m1geo/Quad-AMBE3000/outputs/AMBE3000R-Devices.jpg

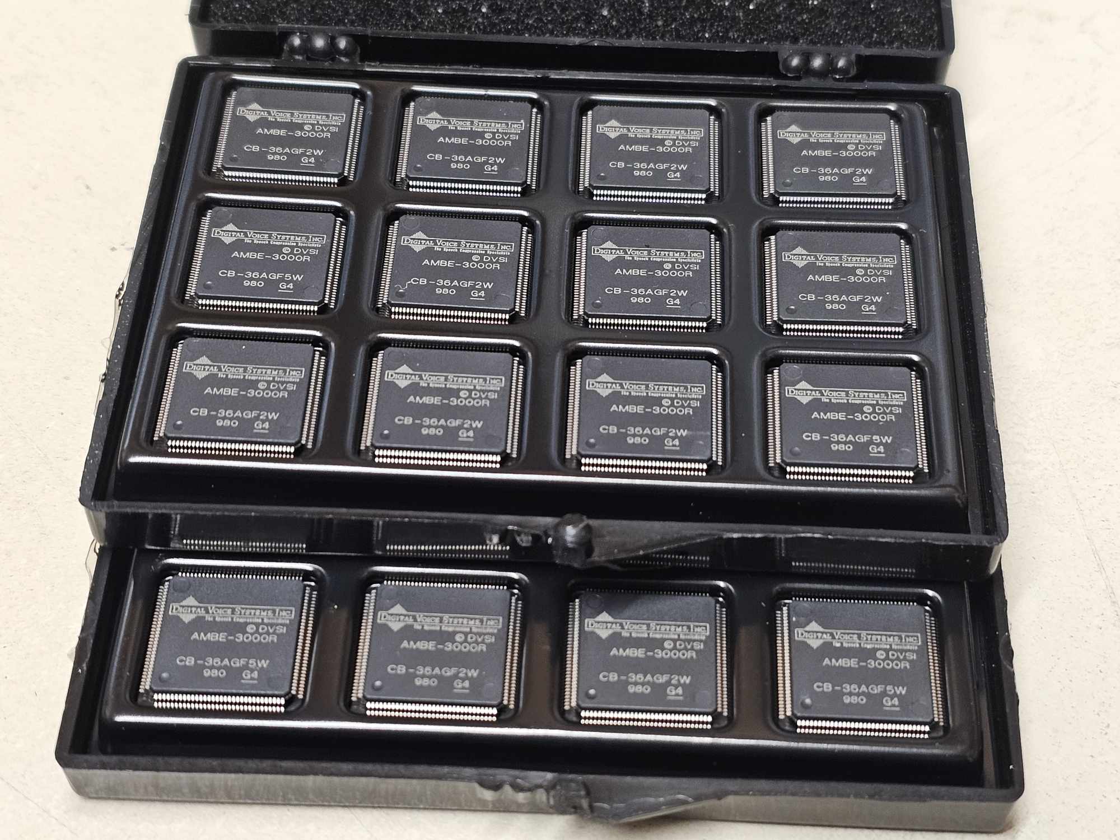
outputs/AMBE3000R-Devices.jpg
